MOSH-Insa-Toulouse/5ISS-Goalard-Lacoste/images/image6.png

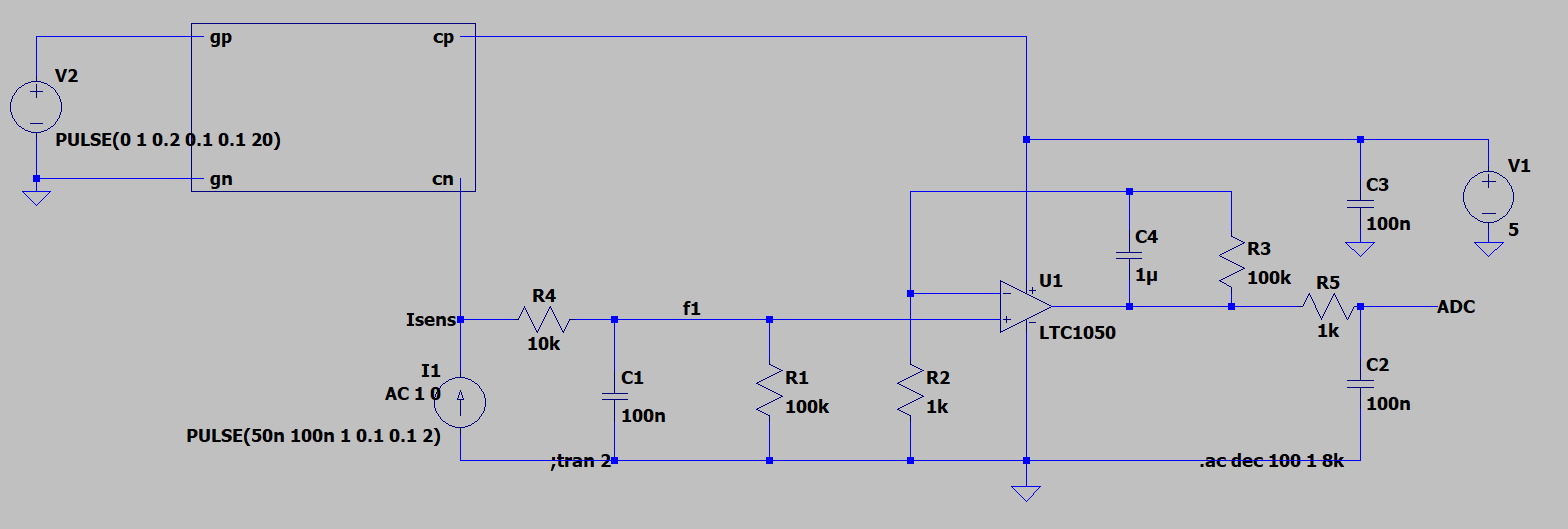
images/image6.png
