MOSH-Insa-Toulouse/5ISS-Goalard-Lacoste/images/image8.png

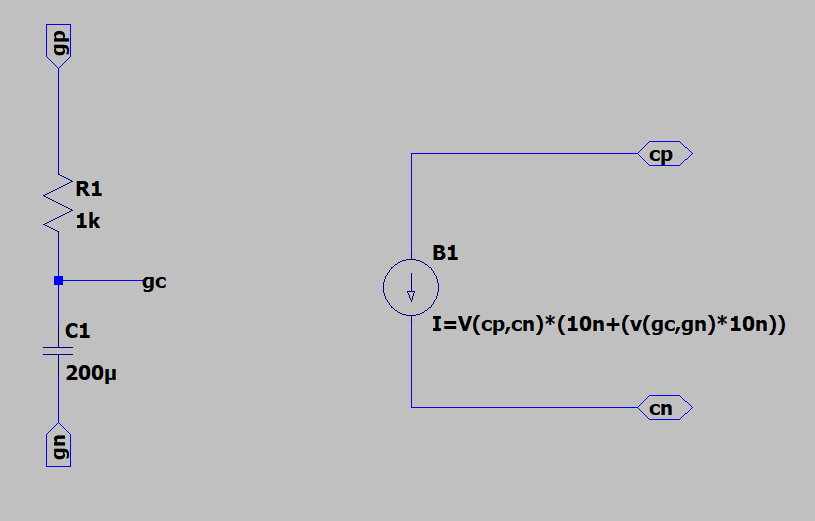
images/image8.png
