MOSH-Insa-Toulouse/5ISS-Goalard-Lacoste/LTSpice/sensor.asc

B1: bi; I=V(cp,cn)*(10n+(v(gc,gn)*10n))
C1: cap; 200µ
R1: res; 1k
Named nets: gc, cn, cp, gp, gn
